petrows/smarthome-galoped-dekad/case/usb-conn.jpg

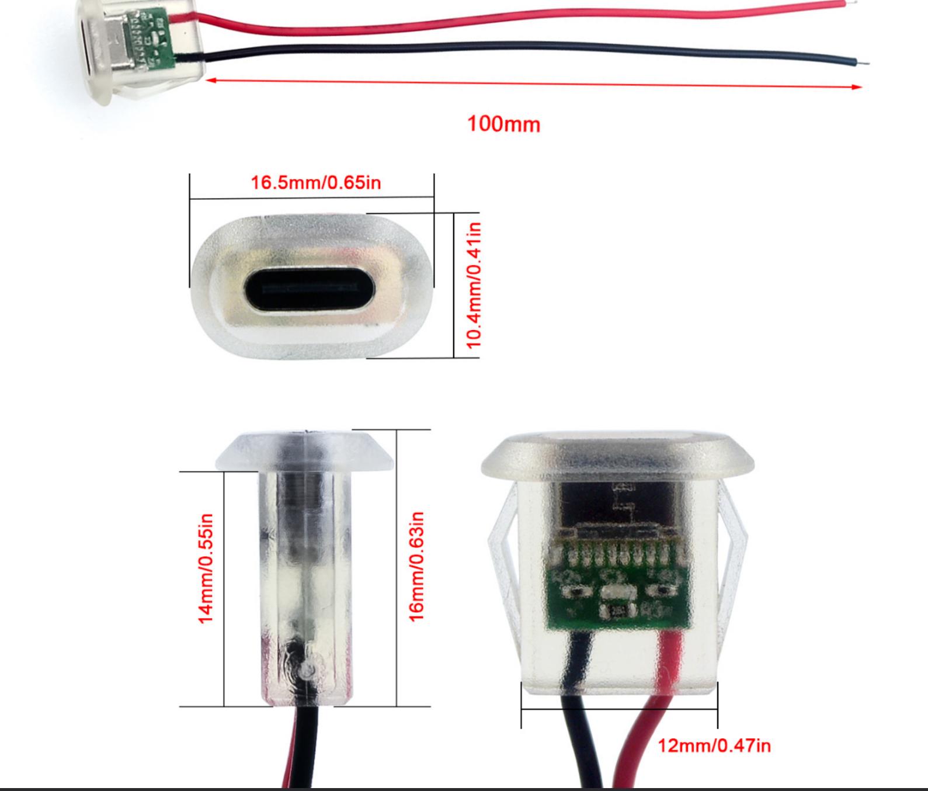
case/usb-conn.jpg
