petrows/smarthome-galoped-dekad/datasheet/BKA30D-R5.webp

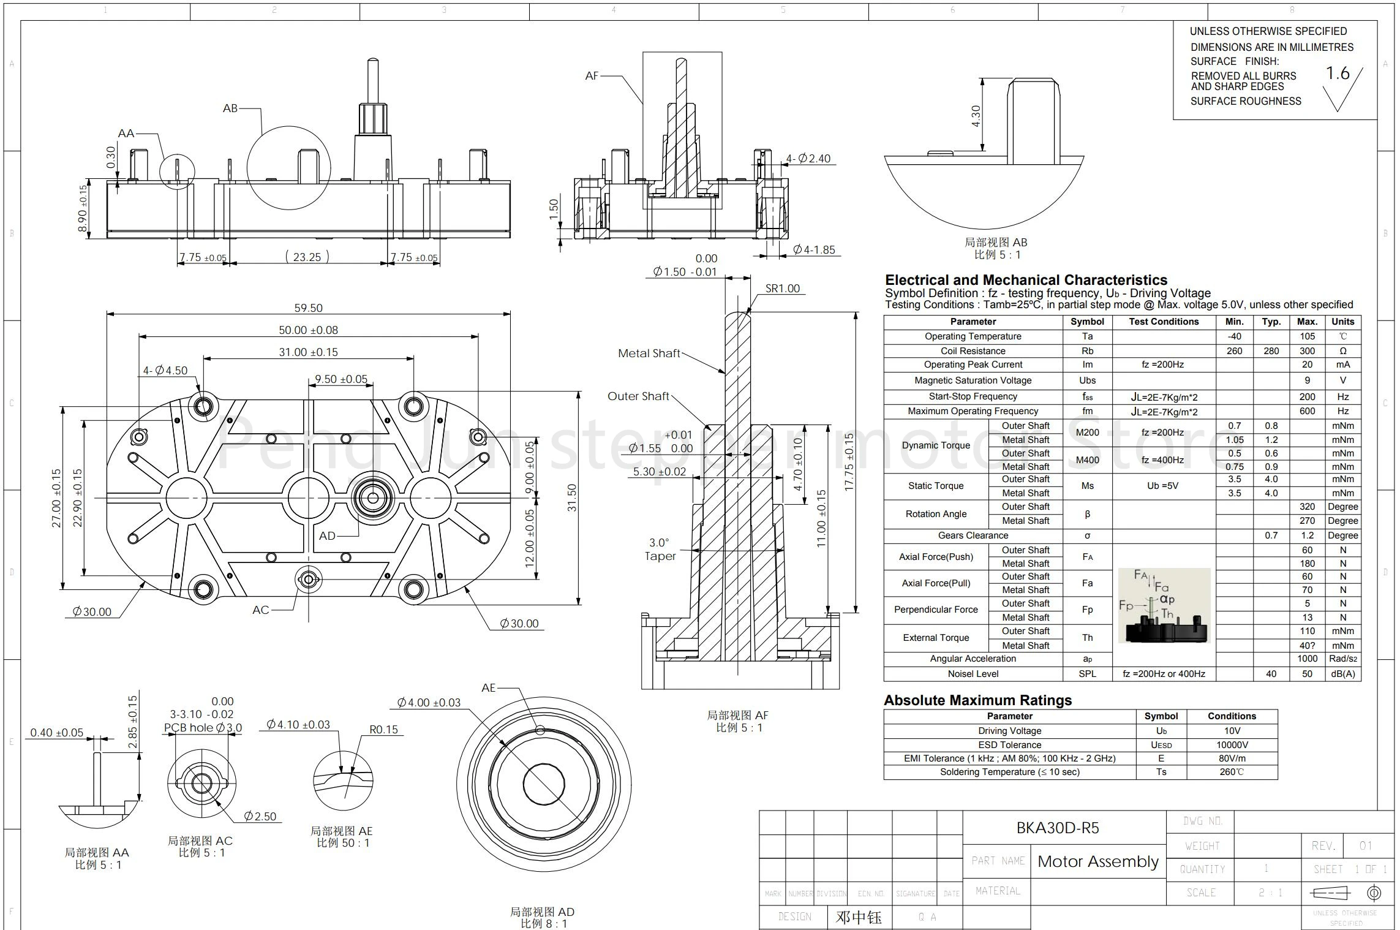
datasheet/BKA30D-R5.webp
