petrows/smarthome-galoped-dekad/datasheet/esp32-c6-supermini.jpg

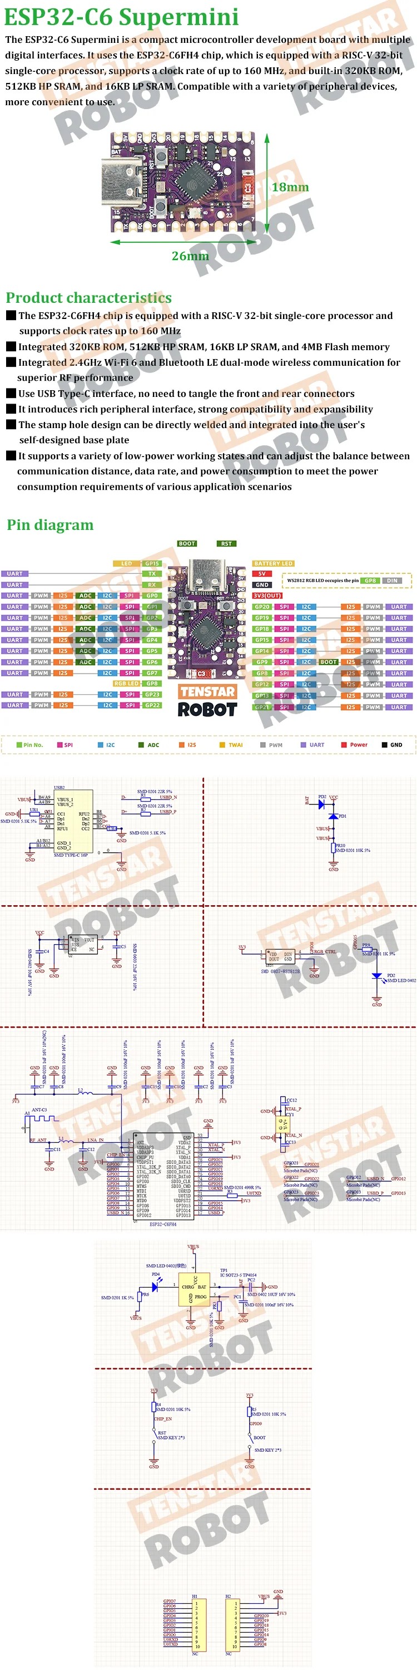
datasheet/esp32-c6-supermini.jpg
