petrows/smarthome-galoped-dekad/datasheet/esp32-h2-supermini.jpg

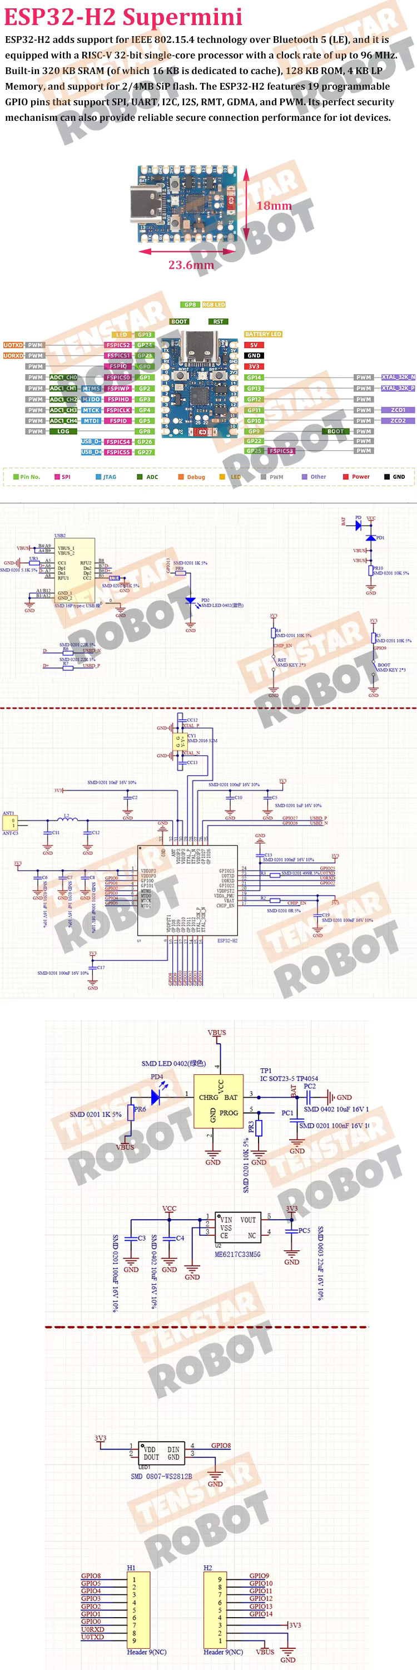
datasheet/esp32-h2-supermini.jpg
