petrows/smarthome-galoped-dekad/gauge/dekad-gauge-perc-270.png

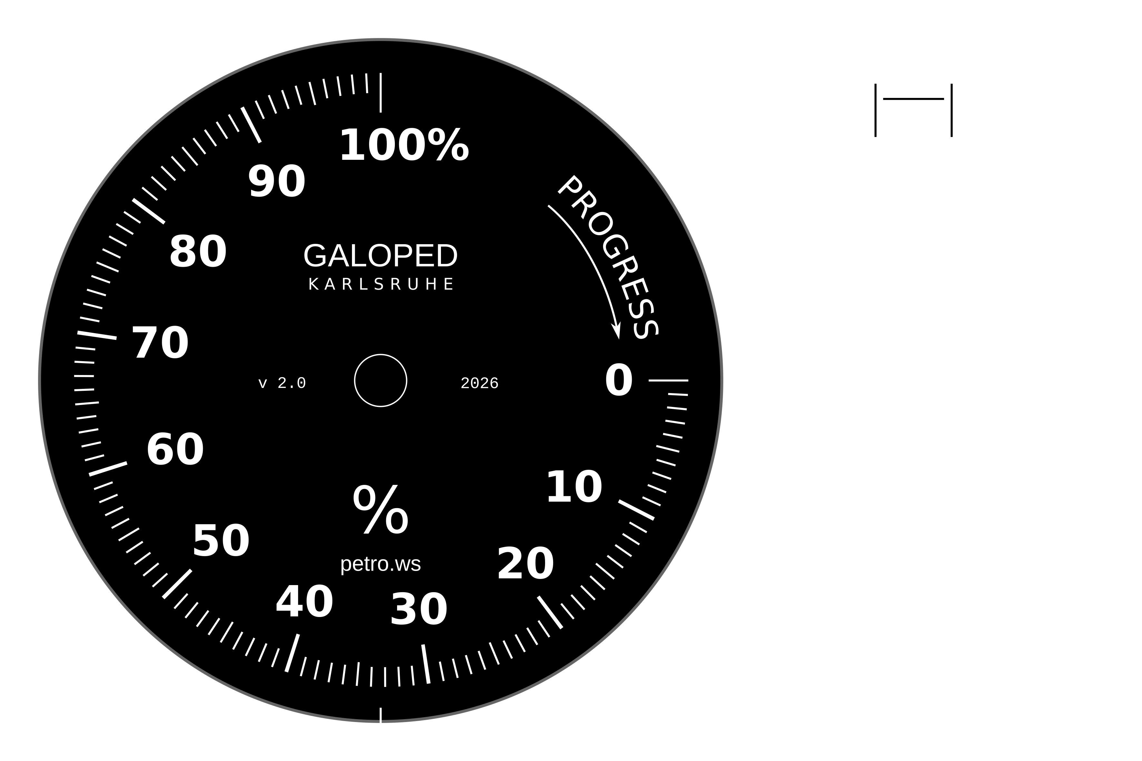
gauge/dekad-gauge-perc-270.png
