petrows/smarthome-galoped-dekad/gauge/dekad-gauge-perc-temp-270.png

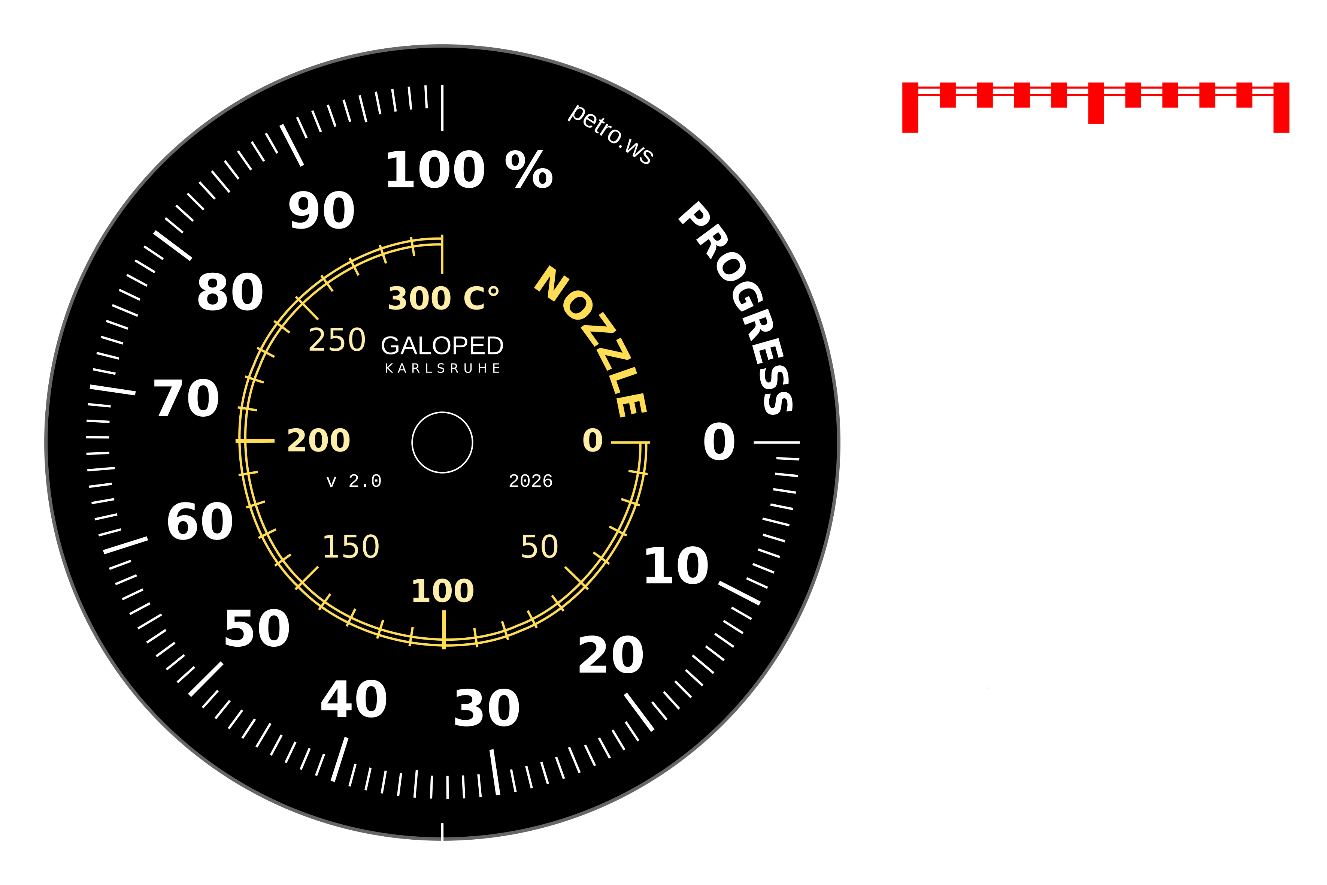
gauge/dekad-gauge-perc-temp-270.png
