petrows/smarthome-galoped-dekad/gauge/dekad-gauge.png

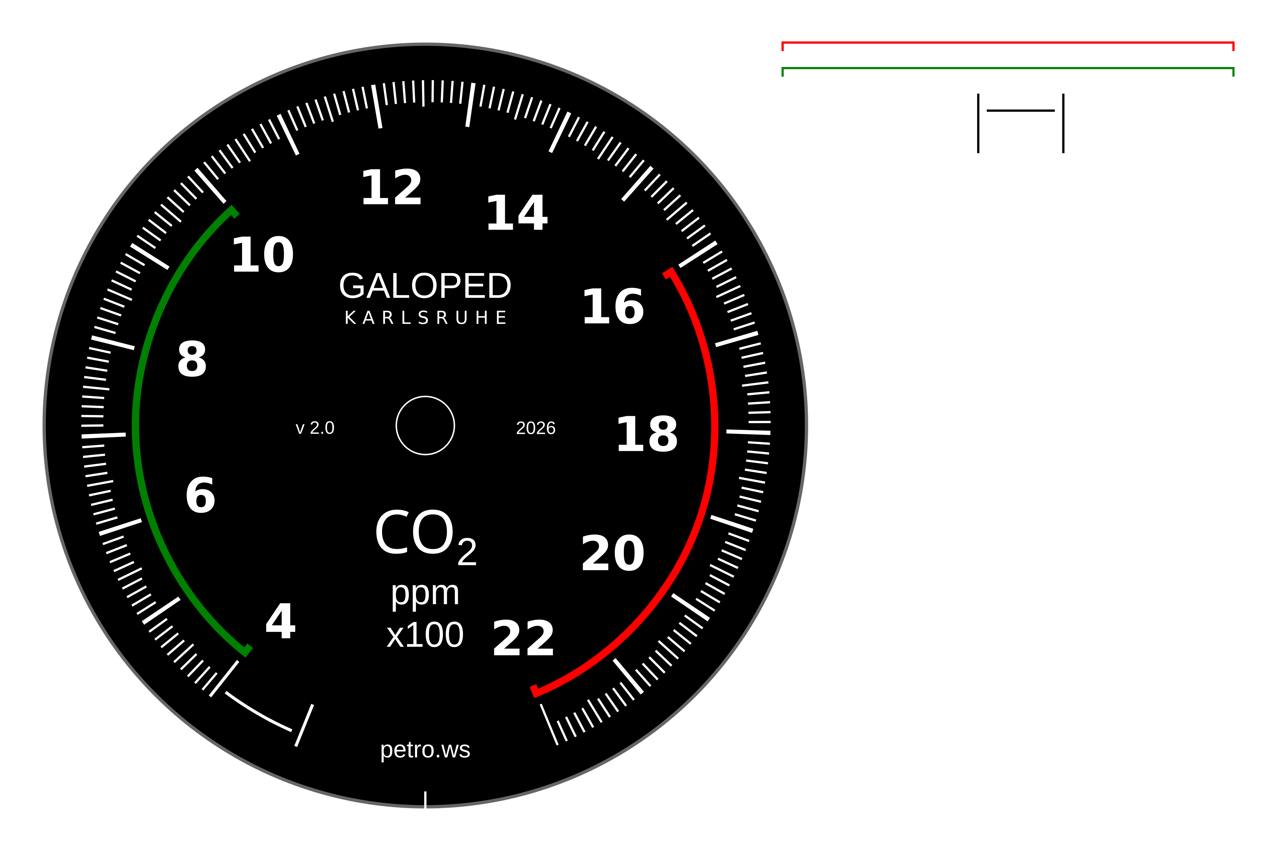
gauge/dekad-gauge.png
