petrows/smarthome-galoped-dekad/schematic/schematic.png

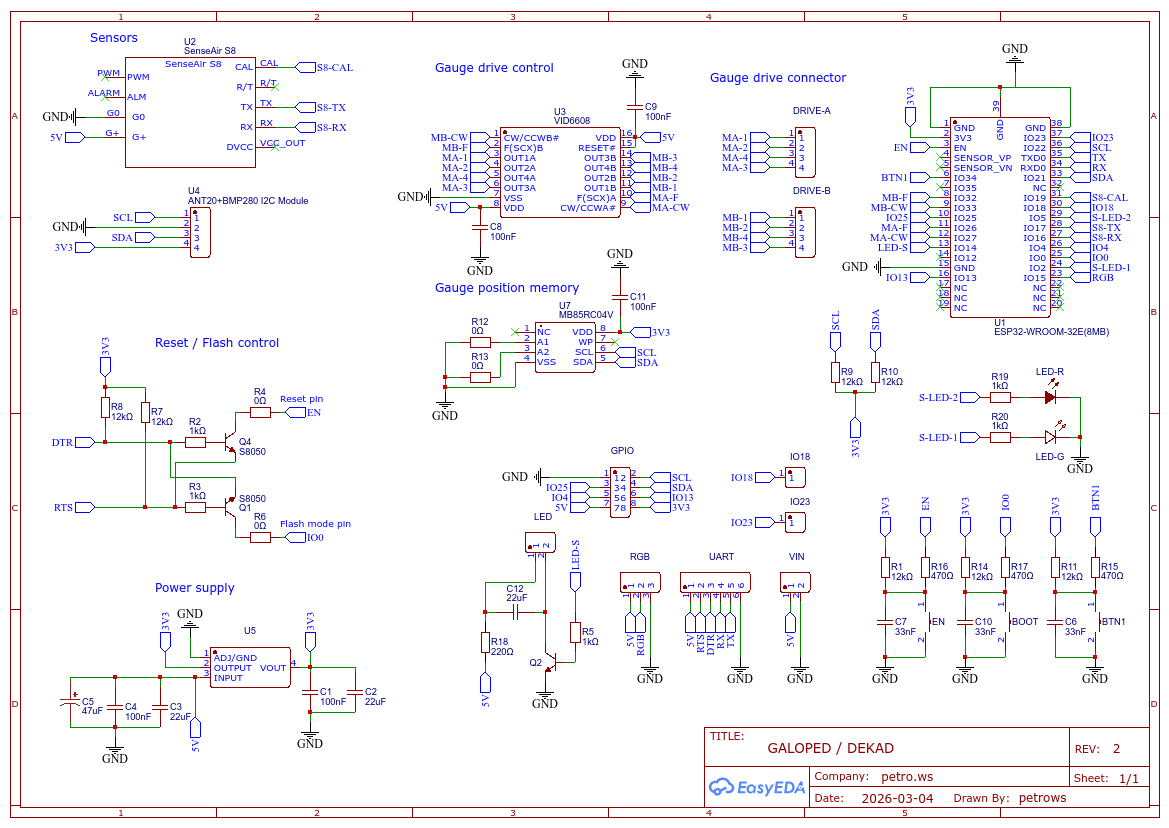
schematic/schematic.png
