petrows/smarthome-galoped-dekad/case/step/drive-single-top.step

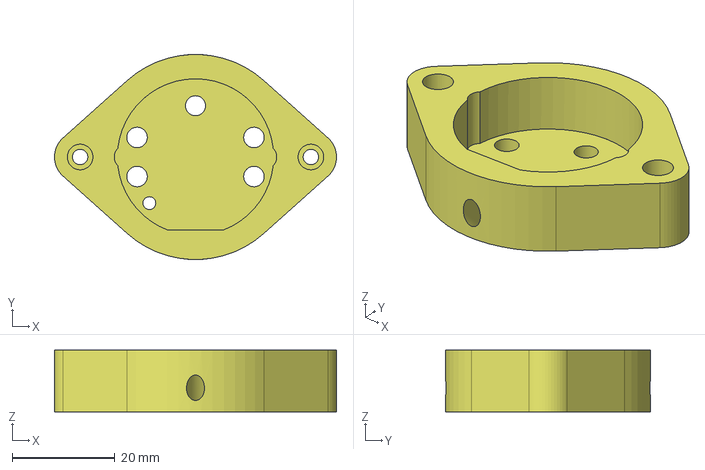
[picture p32: CAD file, 2026-04-06]
case/step/drive-single-top.step
55.0 x 40.0 x 12.0 mm
