petrows/smarthome-galoped-dekad/case/step/drive-double-top.step

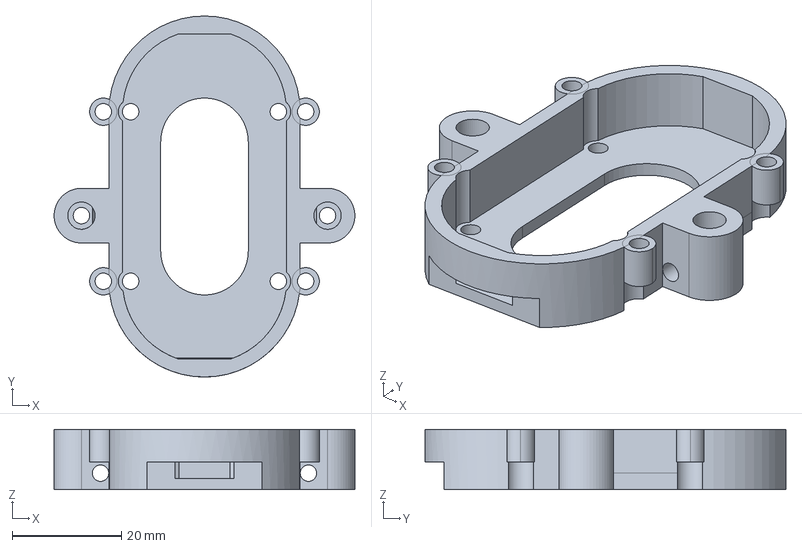
[picture p33: CAD file, 2026-04-06]
case/step/drive-double-top.step
55.0 x 66.0 x 11.0 mm
