petrows/smarthome-galoped-dekad/case/step/top-label.step

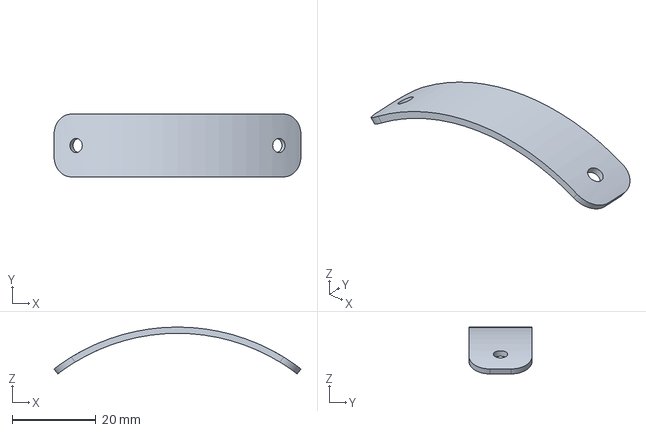
[picture p34: CAD file, 2026-04-06]
case/step/top-label.step
59.0 x 15.0 x 11.2 mm
