petrows/smarthome-galoped-dekad/case/step/arrow-ds-top.step

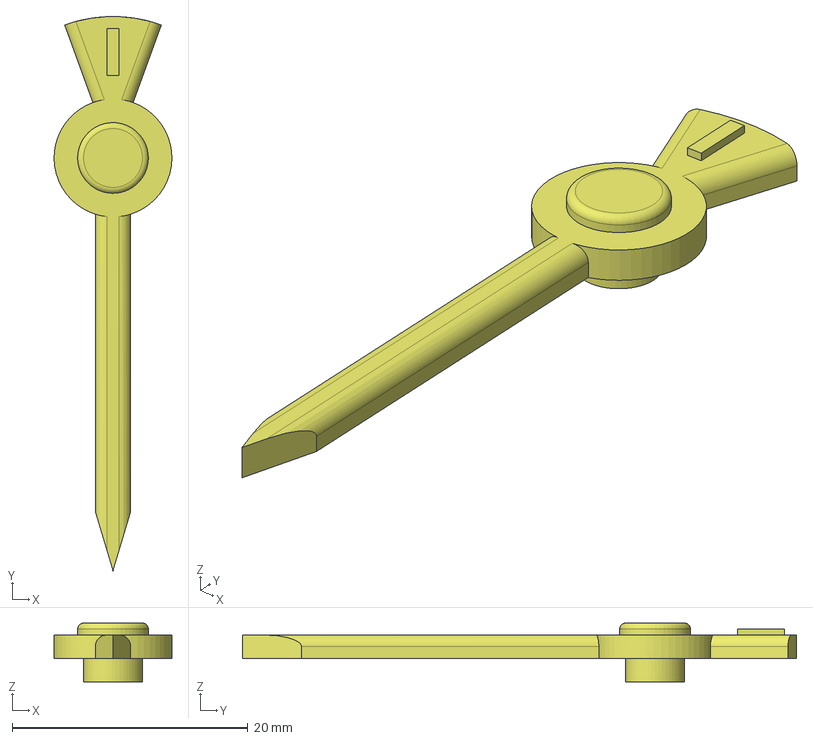
[picture p35: CAD file, 2026-04-06]
case/step/arrow-ds-top.step
10.00 x 47.0 x 5.00 mm
