petrows/smarthome-galoped-dekad/case/step/arrow-double-down.step

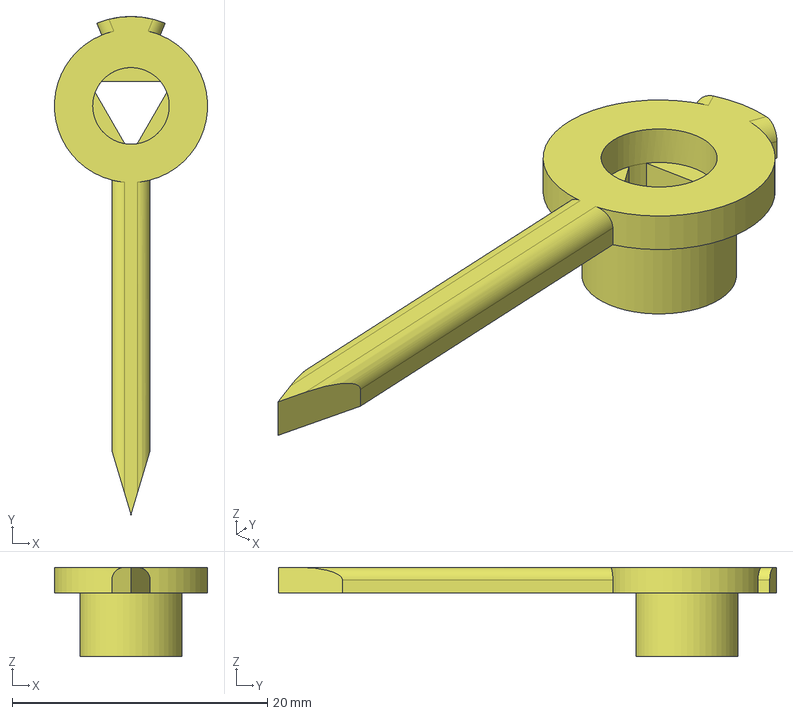
[picture p36: CAD file, 2026-04-06]
case/step/arrow-double-down.step
12.0 x 39.0 x 7.00 mm
