petrows/smarthome-galoped-dekad/case/step/drive-single-offser.step

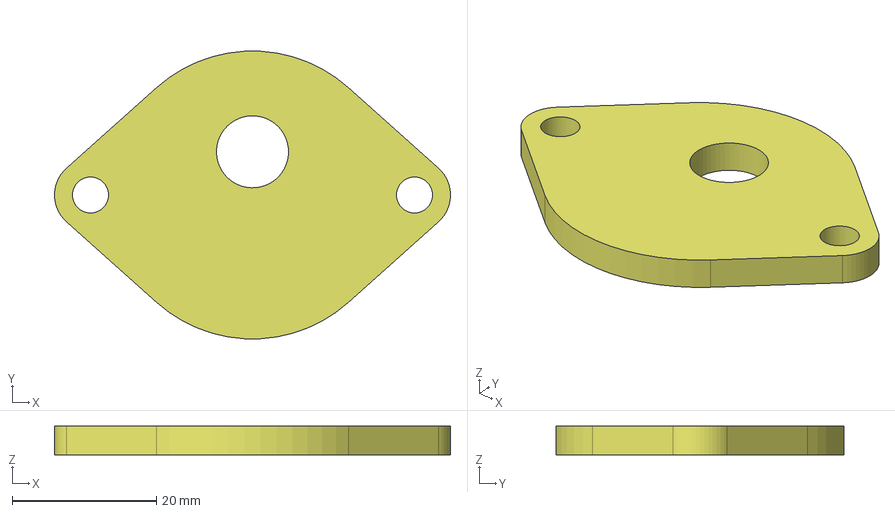
[picture p37: CAD file, 2026-04-06]
case/step/drive-single-offser.step
55.0 x 39.9 x 4.00 mm
