petrows/smarthome-galoped-dekad/case/step/ring-retro.step

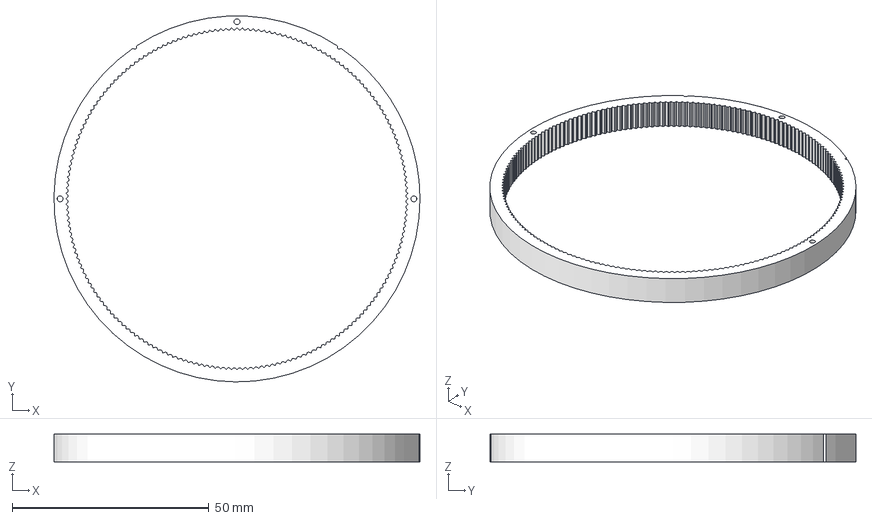
[picture p38: CAD file, 2026-04-06]
case/step/ring-retro.step
93.1 x 93.0 x 7.00 mm
