petrows/smarthome-galoped-dekad/case/step/arrow-ds-alt-top.step

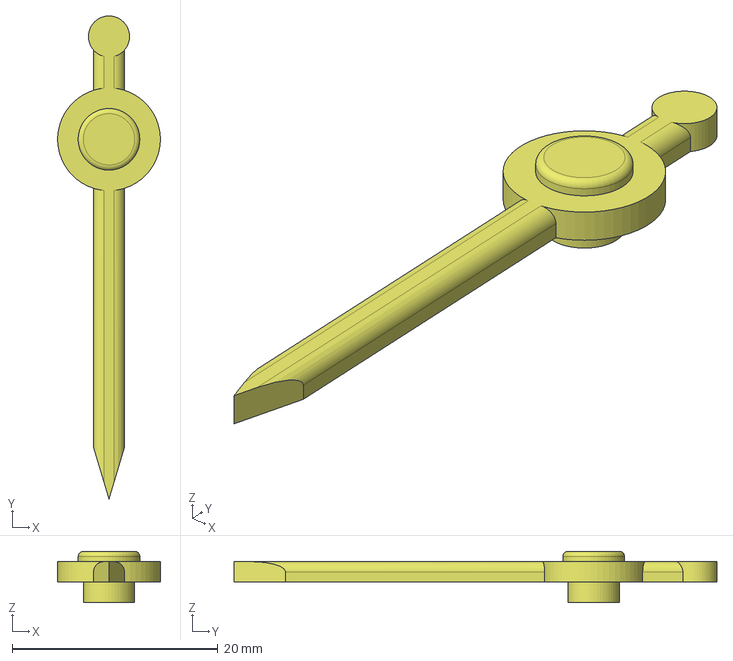
[picture p39: CAD file, 2026-04-06]
case/step/arrow-ds-alt-top.step
9.98 x 47.0 x 5.00 mm
