petrows/smarthome-galoped-dekad/case/step/front.step

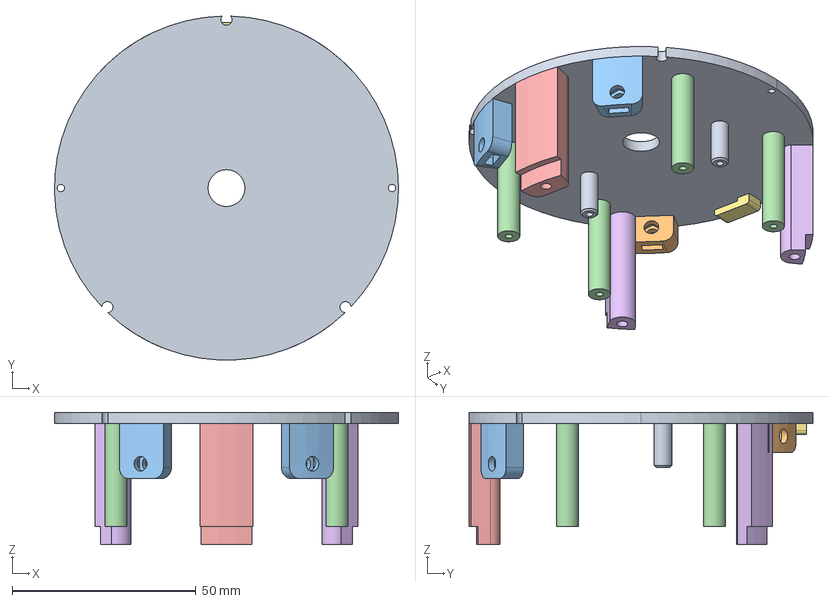
[picture p40: CAD file, 2026-04-06]
case/step/front.step
93.5 x 93.4 x 36.0 mm
Front-top
Leg-b-r
Leg-t-r
Board-holder
Leg-b-l
Leg-t-l
Board-holder-3
Board-holder-2
Board-holder-4
Case-holder-top
Case-holder-bottom-r
Case-holder-bottom-l
Led-wire-holder
