petrows/smarthome-galoped-dekad/case/step/arrow-single.step

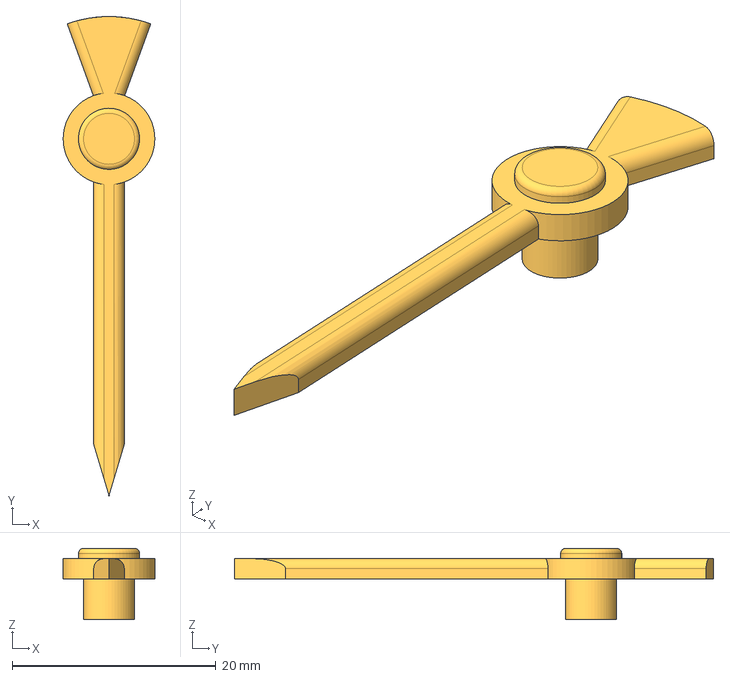
[picture p41: CAD file, 2026-04-06]
case/step/arrow-single.step
9.00 x 47.0 x 7.00 mm
