petrows/smarthome-galoped-dekad/case/step/pcb.step

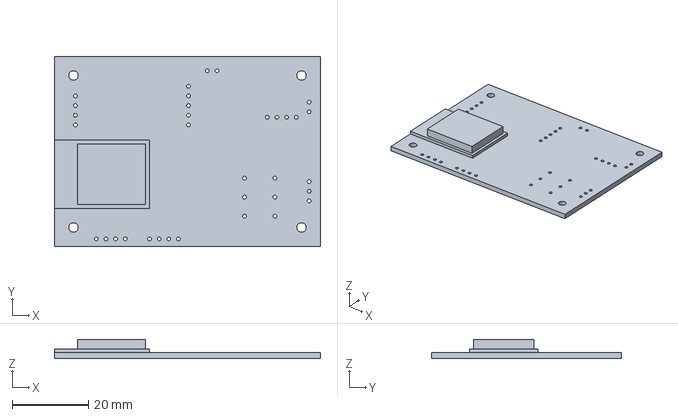
[picture p42: CAD file, 2026-04-06]
case/step/pcb.step
70.0 x 50.0 x 5.10 mm
