petrows/smarthome-galoped-dekad/case/step/galoped-arrow.3mf

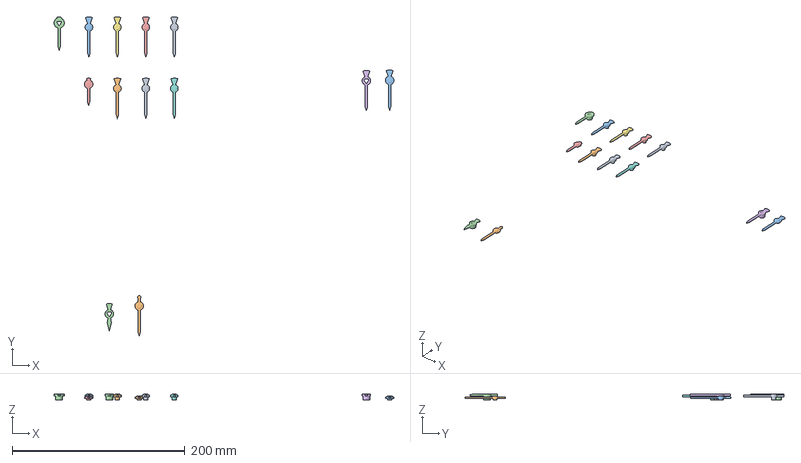
[picture p43: CAD file, 2026-04-06]
case/step/galoped-arrow.3mf
394.2 x 370.1 x 7.50 mm
arrow-single.step x 7
arrow-ds-alt-top.step
Arrow-ds-top
arrow-ds-alt-down.step
Arrow-ds-down
arrow-double-down.step
arrow-double-top.step
