petrows/smarthome-galoped-dekad/case/step/arrow-double-top.step

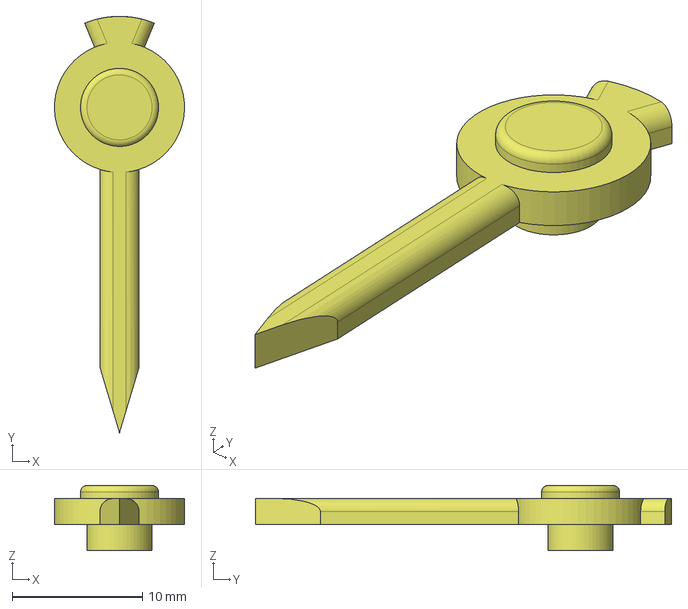
[picture p44: CAD file, 2026-04-06]
case/step/arrow-double-top.step
9.99 x 32.0 x 5.00 mm
