petrows/smarthome-galoped-dekad/doc/assets/assembly-drive.jpg

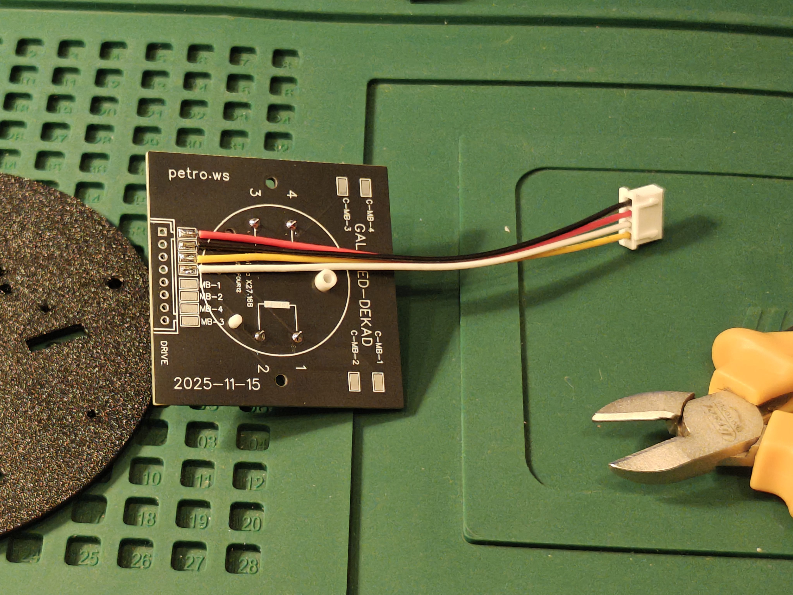
doc/assets/assembly-drive.jpg
