petrows/smarthome-galoped-dekad/firmware-zigbee/galoped/main/rgb_led.cpp

#include "rgb_led.h"

#include "esp_log.h"
#include "led_strip_spi.h"
#include "nvs.h"

#include <cmath>

static const char *TAG = "LED";

namespace
{
constexpr const char *NVS_NS = "rgbled";
constexpr const char *NVS_KEY = "state";
// Bump if PersistedState layout changes — old blobs will be ignored.
constexpr uint32_t SAVE_MAGIC = 0x52474201;  // 'RGB' v1
// Coalesce rapid updates (slider drags emit many writes).
constexpr uint64_t SAVE_DELAY_US = 2'000'000;
}  // namespace

RgbLed::RgbLed(gpio_num_t data_gpio, spi_host_device_t spi_host, uint32_t led_count)
    : pin_(data_gpio),
      spi_host_(spi_host),
      led_count_(led_count),
      strip_(nullptr),
      on_(false),
      brightness_(255),
      color_x_(0x616b),  // ESP_ZB_ZCL_COLOR_CONTROL_CURRENT_X_DEF_VALUE
      color_y_(0x607d),  // ESP_ZB_ZCL_COLOR_CONTROL_CURRENT_Y_DEF_VALUE
      save_timer_(nullptr)
{
}

RgbLed::~RgbLed()
{
    if (save_timer_) {
        // Flush any pending change before tearing down.
        esp_timer_stop(save_timer_);
        save_state();
        esp_timer_delete(save_timer_);
    }
    if (strip_) {
        led_strip_del(strip_);
    }
}

esp_err_t RgbLed::init()
{
    led_strip_config_t strip_cfg = {};
    strip_cfg.strip_gpio_num = pin_;
    strip_cfg.max_leds = led_count_;
    strip_cfg.led_model = LED_MODEL_WS2812;
    strip_cfg.color_component_format = LED_STRIP_COLOR_COMPONENT_FMT_GRB;
    strip_cfg.flags.invert_out = false;

    led_strip_spi_config_t spi_cfg = {};
    spi_cfg.clk_src = SPI_CLK_SRC_DEFAULT;
    spi_cfg.spi_bus = spi_host_;
    spi_cfg.flags.with_dma = true;

    esp_err_t err = led_strip_new_spi_device(&strip_cfg, &spi_cfg, &strip_);
    if (err != ESP_OK) {
        ESP_LOGE(TAG, "led_strip_new_spi_device: %s", esp_err_to_name(err));
        return err;
    }

    led_strip_clear(strip_);
    ESP_LOGI(TAG, "init gpio=%d host=%d leds=%lu", pin_, spi_host_, (unsigned long)led_count_);

    esp_timer_create_args_t targs = {};
    targs.callback = &RgbLed::save_cb;
    targs.dispatch_method = ESP_TIMER_TASK;
    targs.arg = this;
    targs.name = "rgb_save";
    if (esp_timer_create(&targs, &save_timer_) != ESP_OK) {
        ESP_LOGW(TAG, "save timer create failed; persistence disabled");
        save_timer_ = nullptr;
    }

    if (load_state() == ESP_OK) {
        render();  // restore the saved appearance immediately
    }
    return ESP_OK;
}

esp_err_t RgbLed::load_state()
{
    nvs_handle_t h;
    esp_err_t err = nvs_open(NVS_NS, NVS_READONLY, &h);
    if (err != ESP_OK) {
        // Namespace doesn't exist on first boot — silent.
        return err;
    }
    PersistedState s = {};
    size_t sz = sizeof(s);
    err = nvs_get_blob(h, NVS_KEY, &s, &sz);
    nvs_close(h);

    if (err != ESP_OK || sz != sizeof(s) || s.magic != SAVE_MAGIC) {
        return ESP_ERR_NOT_FOUND;
    }
    on_ = s.on;
    brightness_ = s.brightness;
    color_x_ = s.color_x;
    color_y_ = s.color_y;
    ESP_LOGI(TAG, "restored: on=%d bri=%u xy=%u,%u", on_, brightness_, color_x_, color_y_);
    return ESP_OK;
}

esp_err_t RgbLed::save_state()
{
    nvs_handle_t h;
    esp_err_t err = nvs_open(NVS_NS, NVS_READWRITE, &h);
    if (err != ESP_OK) {
        ESP_LOGW(TAG, "nvs_open(rw): %s", esp_err_to_name(err));
        return err;
    }
    PersistedState s = {SAVE_MAGIC, on_, brightness_, color_x_, color_y_};
    err = nvs_set_blob(h, NVS_KEY, &s, sizeof(s));
    if (err == ESP_OK) {
        err = nvs_commit(h);
    }
    nvs_close(h);
    if (err != ESP_OK) {
        ESP_LOGW(TAG, "save failed: %s", esp_err_to_name(err));
    }
    return err;
}

void RgbLed::schedule_save()
{
    if (!save_timer_)
        return;
    // Restart the one-shot so a burst of writes coalesces into a single flush
    // SAVE_DELAY_US after the last change.
    esp_timer_stop(save_timer_);
    esp_timer_start_once(save_timer_, SAVE_DELAY_US);
}

void RgbLed::save_cb(void *arg)
{
    static_cast<RgbLed *>(arg)->save_state();
}

void RgbLed::set_on(bool on)
{
    on_ = on;
    render();
    schedule_save();
}

void RgbLed::set_brightness(uint8_t brightness)
{
    brightness_ = brightness;
    render();
    schedule_save();
}

void RgbLed::set_xy(uint16_t color_x, uint16_t color_y)
{
    color_x_ = color_x;
    color_y_ = color_y;
    render();
    schedule_save();
}

void RgbLed::render()
{
    if (!strip_) {
        return;
    }
    if (!on_ || brightness_ == 0) {
        led_strip_clear(strip_);
        return;
    }

    uint8_t r, g, b;
    xy_to_rgb(color_x_, color_y_, brightness_, r, g, b);

    for (uint32_t i = 0; i < led_count_; ++i) {
        led_strip_set_pixel(strip_, i, r, g, b);
    }
    led_strip_refresh(strip_);
}

void RgbLed::xy_to_rgb(uint16_t x16, uint16_t y16, uint8_t bri, uint8_t &r, uint8_t &g, uint8_t &b)
{
    // Zigbee CurrentX/Y are uint16 representing CIE 1931 chromaticity 0..1.
    // Convert at unit luminance, normalize the channel max to 1, *then* apply
    // brightness — otherwise saturated chromaticities clip in gamma() and
    // brightness only has effect over a narrow low-end window.
    float x = x16 / 65535.0f;
    float y = y16 / 65535.0f;
    if (y < 1e-4f) {
        y = 1e-4f;
    }
    float X = x / y;
    float Z = (1.0f - x - y) / y;

    // CIE XYZ -> linear sRGB (D65), with Y = 1
    float lr = X * 3.2404542f - 1.5371385f - Z * 0.4985314f;
    float lg = -X * 0.9692660f + 1.8760108f + Z * 0.0415560f;
    float lb = X * 0.0556434f - 0.2040259f + Z * 1.0572252f;

    if (lr < 0.0f)
        lr = 0.0f;
    if (lg < 0.0f)
        lg = 0.0f;
    if (lb < 0.0f)
        lb = 0.0f;

    float m = lr;
    if (lg > m)
        m = lg;
    if (lb > m)
        m = lb;
    if (m > 1.0f) {
        lr /= m;
        lg /= m;
        lb /= m;
    }

    float bf = bri / 255.0f;
    lr *= bf;
    lg *= bf;
    lb *= bf;

    auto gamma = [](float v) -> float {
        if (v <= 0.0f) {
            return 0.0f;
        }
        if (v >= 1.0f) {
            return 1.0f;
        }
        return v <= 0.0031308f ? 12.92f * v : 1.055f * powf(v, 1.0f / 2.4f) - 0.055f;
    };

    r = static_cast<uint8_t>(gamma(lr) * 255.0f + 0.5f);
    g = static_cast<uint8_t>(gamma(lg) * 255.0f + 0.5f);
    b = static_cast<uint8_t>(gamma(lb) * 255.0f + 0.5f);
}
